Ironman-007/Digital_Artifact/Firmware/MC_V1/src/MC_encoder_FZ.h

#pragma once

#include <Arduino.h>

#include "MC_system_FZ.h"

#define ENCODER_1_PIN 19
#define ENCODER_2_PIN 22

extern long encoder_count;

extern void MC_encoder_init(void);
extern void MC_read_encoder(void);
