Ironman-007/Digital_Artifact/Firmware/MC_V1/src/MC_joystick_FZ.cpp

#include "MC_joystick_FZ.h"

int joystickX = 0;
int joystickY = 0;

void MC_joystickInit()
{
  pinMode(JOYSTICK_X_PIN, INPUT);
  pinMode(JOYSTICK_Y_PIN, INPUT);
}

void MC_joystickRead()
{
  joystickX = analogRead(JOYSTICK_X_PIN);
  joystickY = analogRead(JOYSTICK_Y_PIN);
}
